anton2785-bit/Anton-s-Split-keyboard/Images/PCB in PCB editor.png

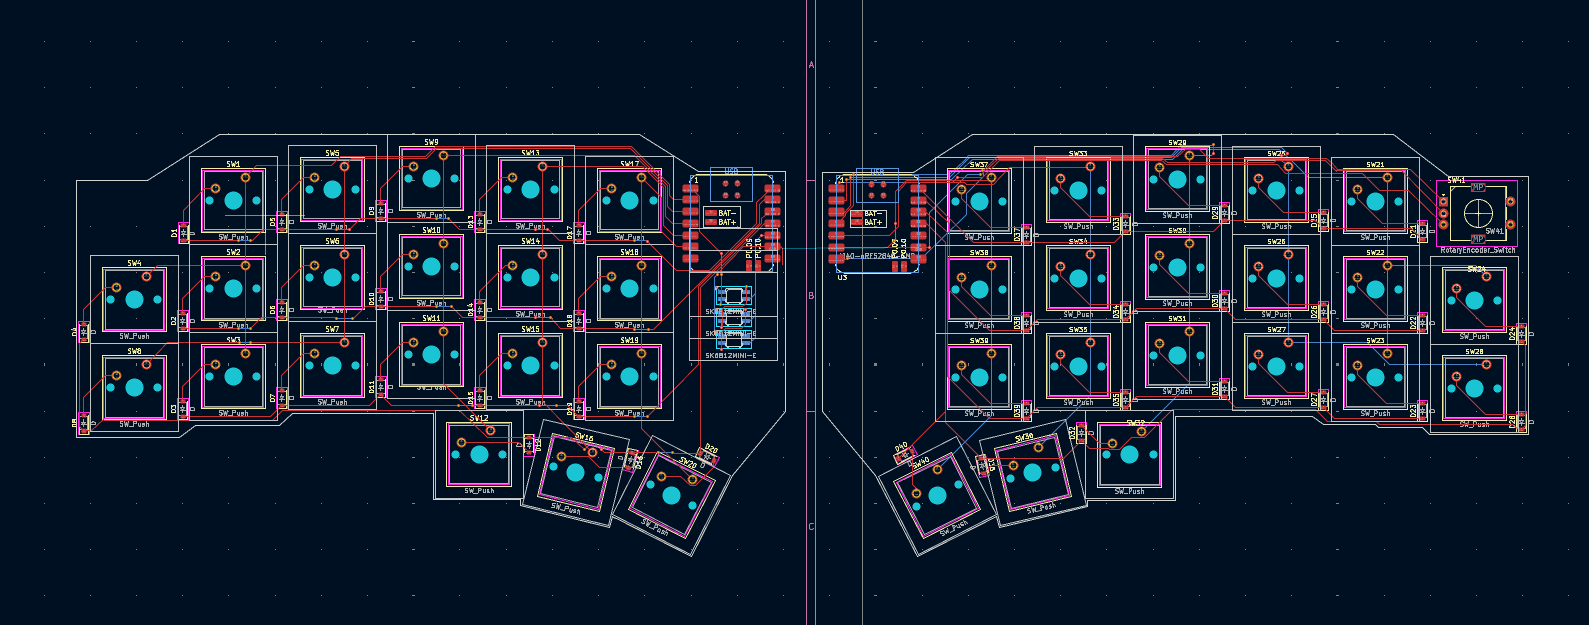
Images/PCB in PCB editor.png
