anton2785-bit/Anton-s-Split-keyboard/Images/3D model assembly.png

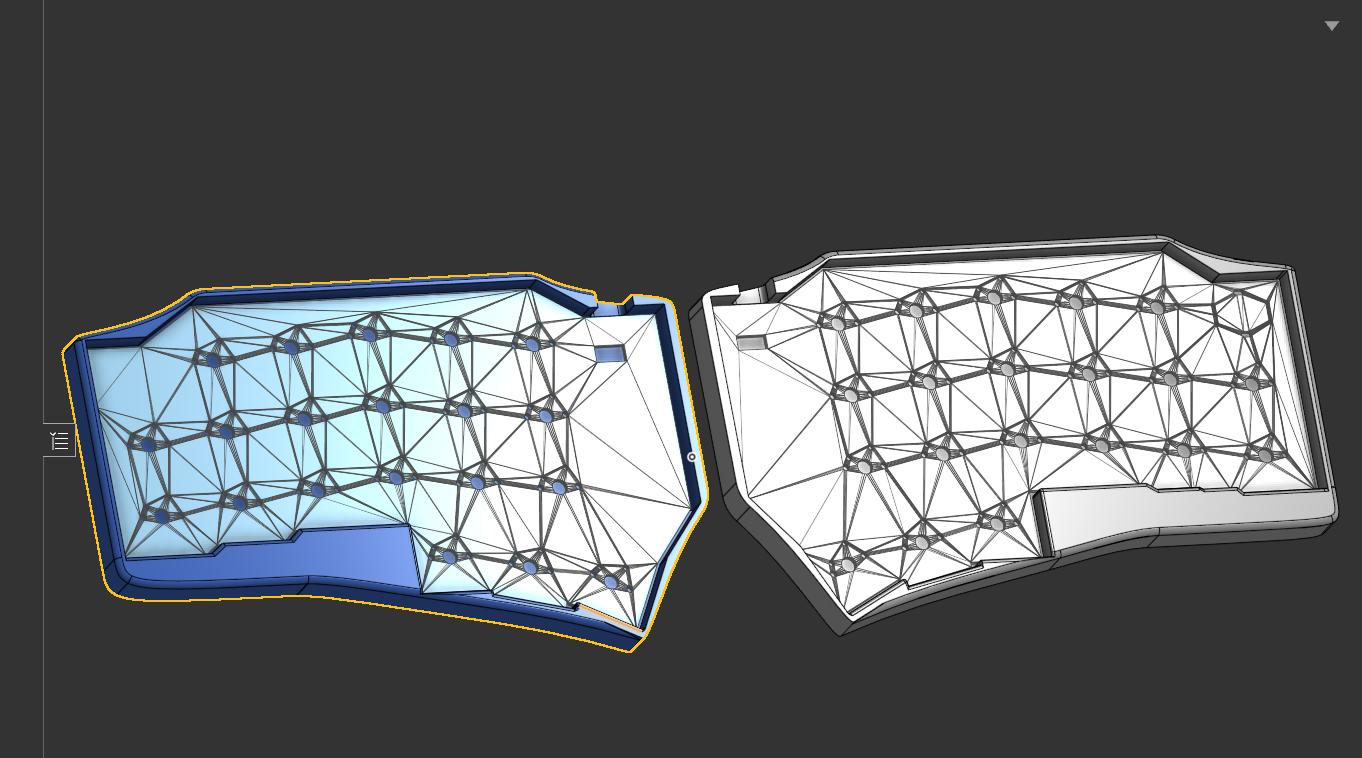
Images/3D model assembly.png
